na103/MatshitaPico/img/beta_assembly/02_beta_assembly.jpg

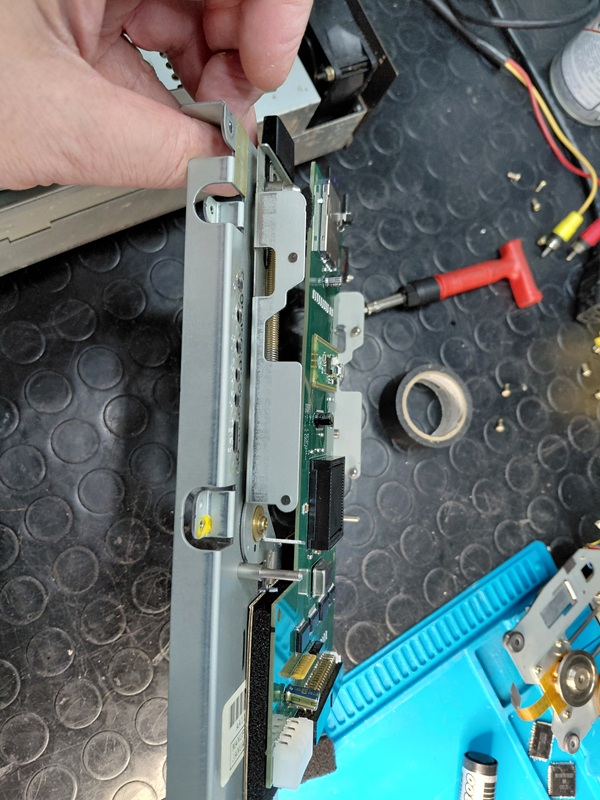
img/beta_assembly/02_beta_assembly.jpg
