na103/MatshitaPico/img/beta_assembly/03_beta_assembly.jpg

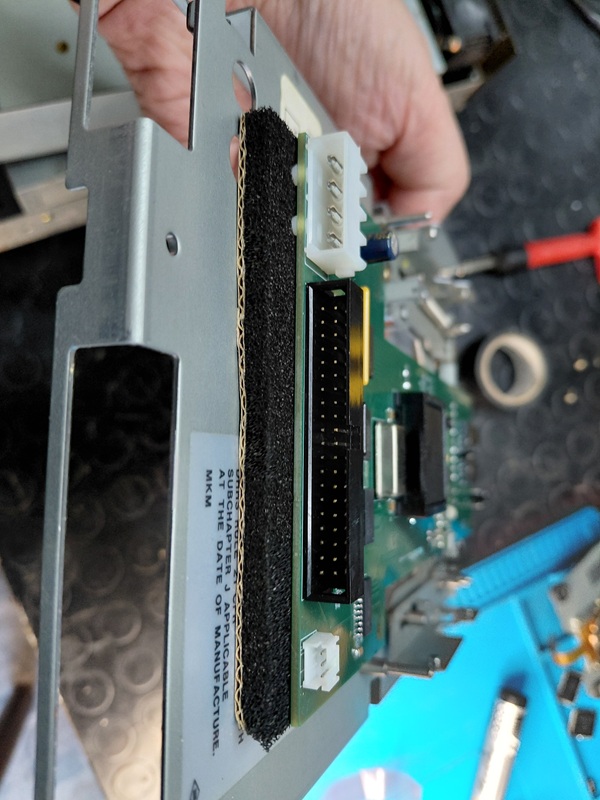
img/beta_assembly/03_beta_assembly.jpg
